Harveyn4444/cubesat-reaction-wheel/assets/img/motor-encoder.png

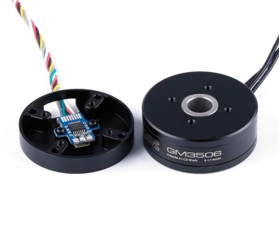
assets/img/motor-encoder.png
