Harveyn4444/cubesat-reaction-wheel/assets/img/mpu6050.jpeg

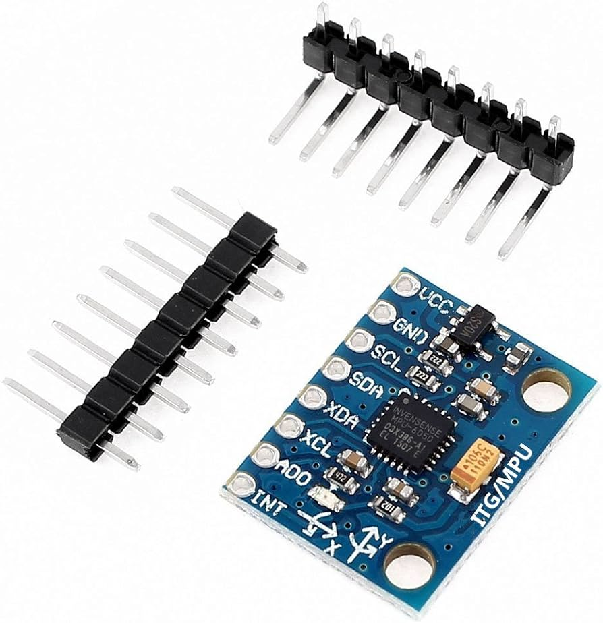
assets/img/mpu6050.jpeg
