Harveyn4444/cubesat-reaction-wheel/assets/img/teensy4.jpeg

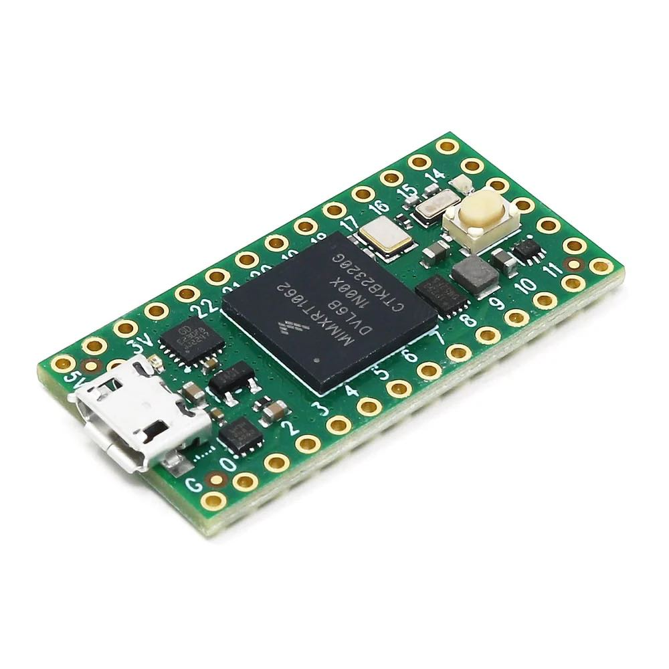
assets/img/teensy4.jpeg
