Harveyn4444/cubesat-reaction-wheel/assets/img/wheel.png

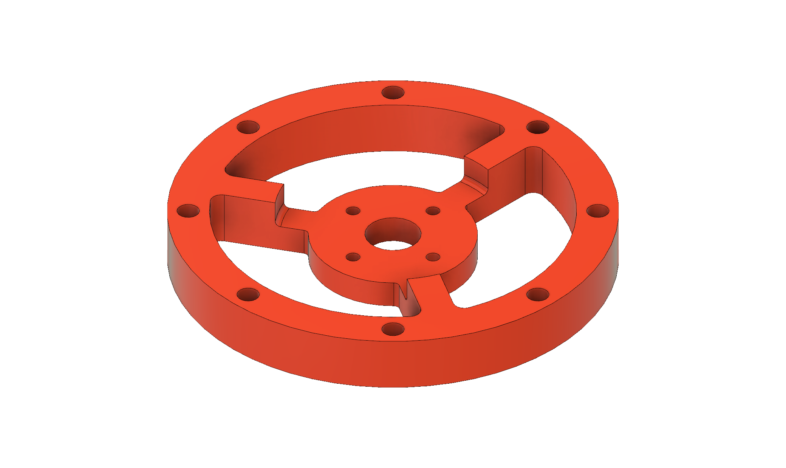
assets/img/wheel.png
