Harveyn4444/cubesat-reaction-wheel/code/data-logging/data/open-loop-rc/open-loop-velocity.png

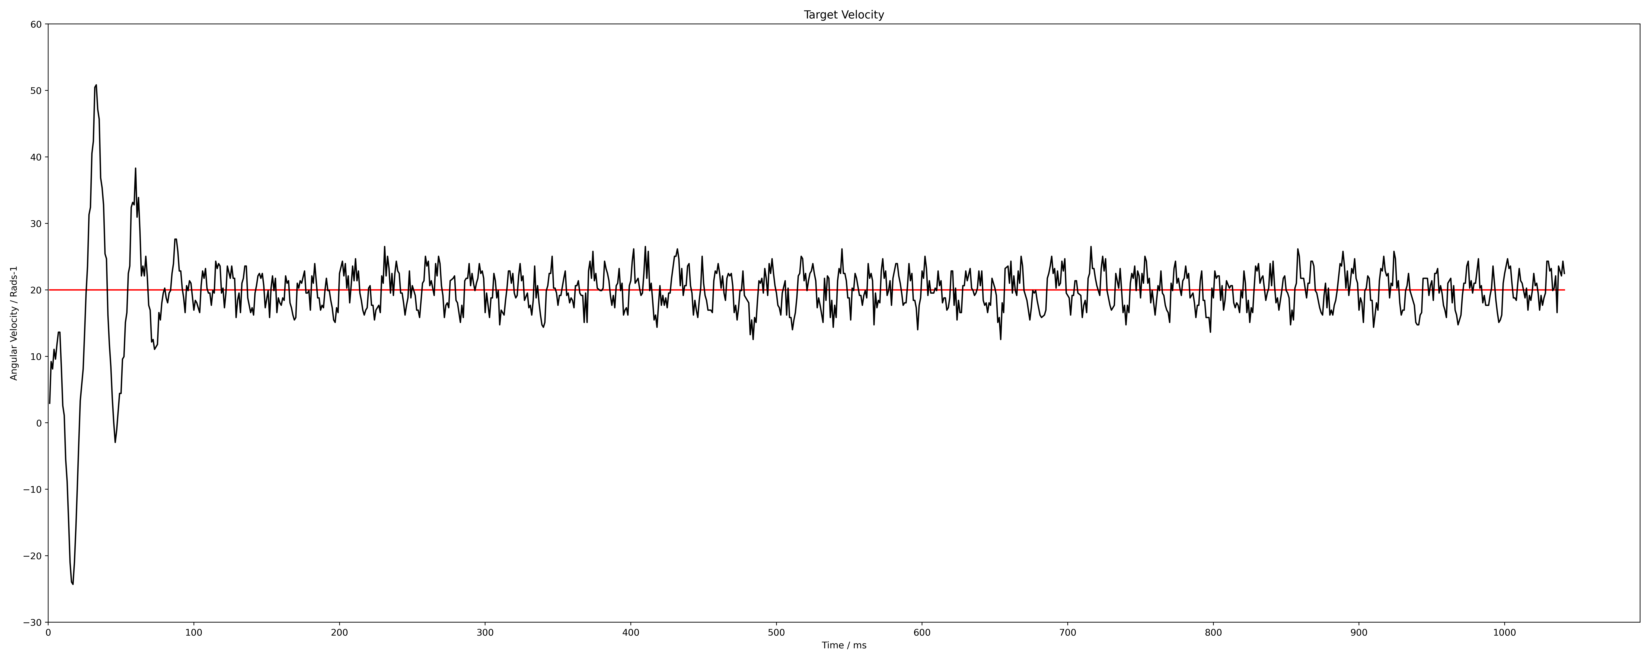
code/data-logging/data/open-loop-rc/open-loop-velocity.png
