Harveyn4444/cubesat-reaction-wheel/code/data-logging/data/pid-velocity/pid-1-0-0.png

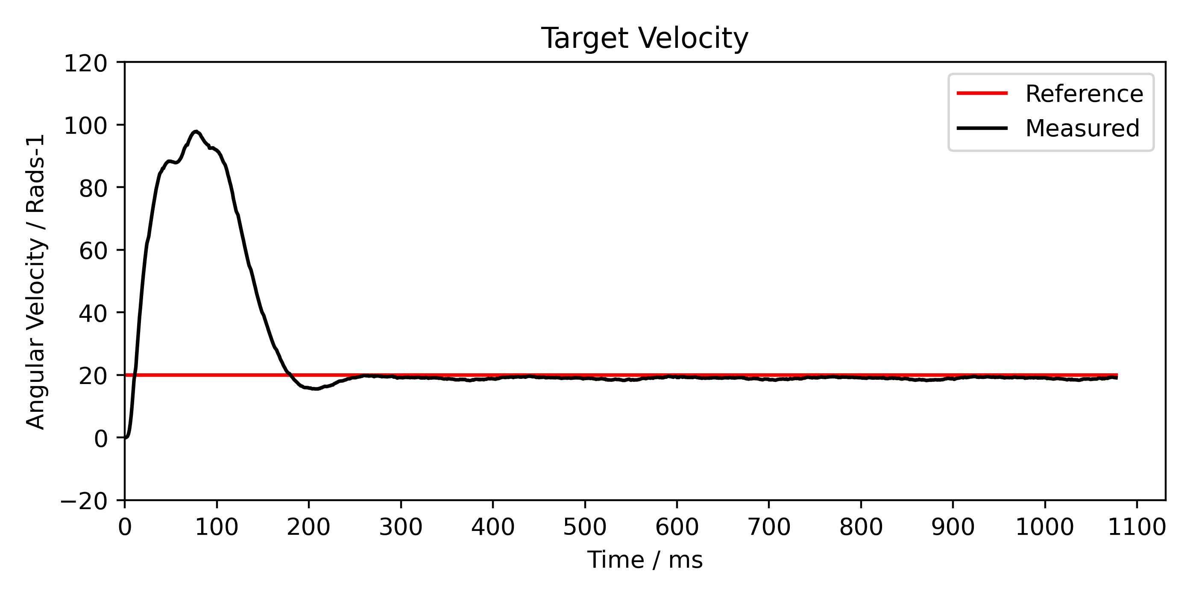
code/data-logging/data/pid-velocity/pid-1-0-0.png
