Harveyn4444/cubesat-reaction-wheel/code/data-logging/data/pid-velocity/pid-1-10-0.png

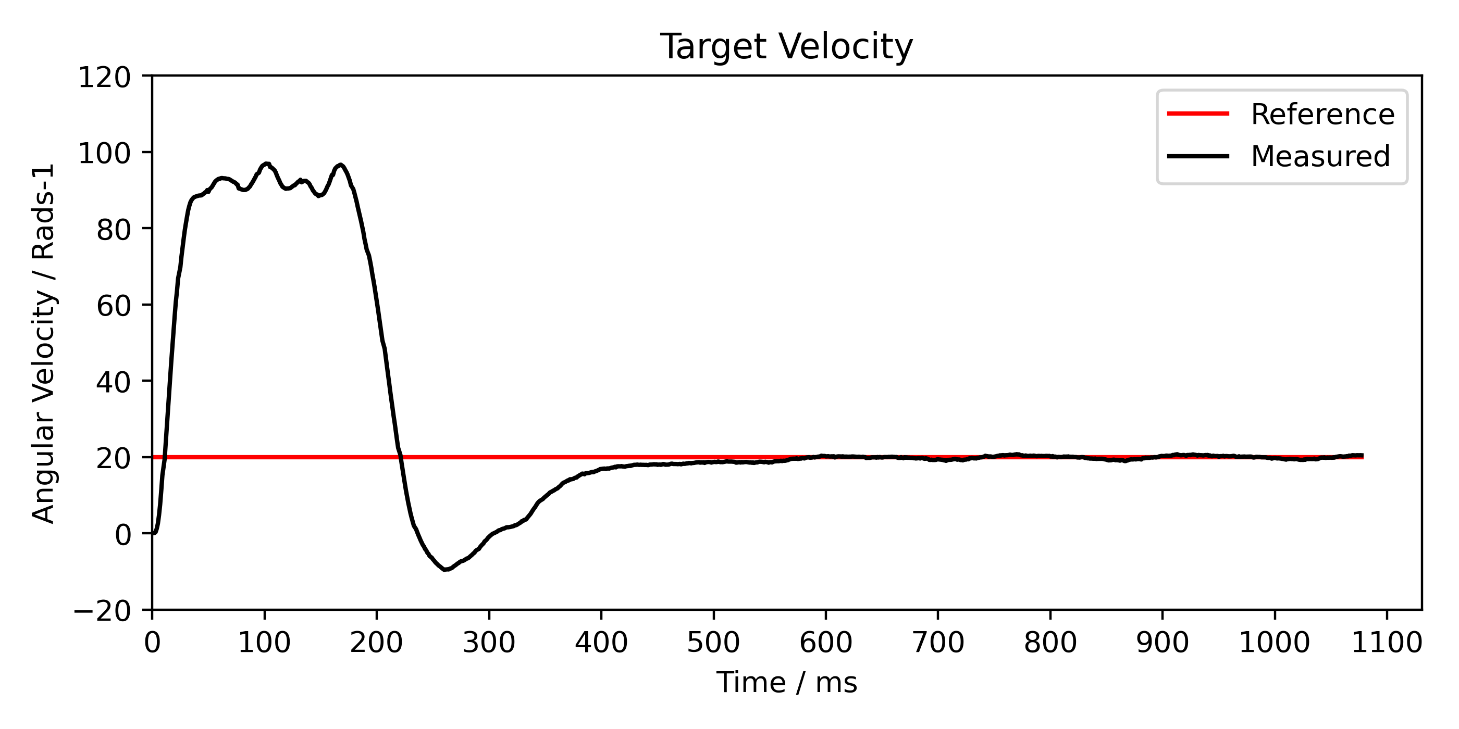
code/data-logging/data/pid-velocity/pid-1-10-0.png
