Harveyn4444/cubesat-reaction-wheel/code/data-logging/data/pid-torque/measured-torque-test-2.csv

Time | TargetVelocity | TargetTorque | Measured | Error | alpha | torque
0 | 20.00 | 0.1899 | 0.00 | 20.00 | 0.0006 | 0.0015
1 | 20.00 | 0.1899 | 0.00 | 20.00 | -0.0001 | -0.0002
2 | 20.00 | 0.1899 | 0.00 | 20.00 | -0.0001 | -0.0001
3 | 20.00 | 0.1899 | 0.11 | 19.89 | 0.0266 | 0.0638
4 | 20.00 | 0.1899 | 0.24 | 19.76 | 0.0328 | 0.0787
5 | 20.00 | 0.1899 | 0.39 | 19.61 | 0.0384 | 0.0921
6 | 20.00 | 0.1899 | 0.57 | 19.43 | 0.0434 | 0.1042
7 | 20.00 | 0.1899 | 0.58 | 19.42 | 0.0036 | 0.0086
8 | 20.00 | 0.1899 | 0.95 | 19.05 | 0.0920 | 0.2208
9 | 20.00 | 0.1899 | 1.21 | 18.79 | 0.0650 | 0.1561
11 | 20.00 | 0.1899 | 1.34 | 18.66 | 0.0319 | 0.0766
12 | 20.00 | 0.1899 | 1.66 | 18.34 | 0.0820 | 0.1967
13 | 20.00 | 0.1899 | 1.85 | 18.15 | 0.0472 | 0.1132
14 | 20.00 | 0.1899 | 2.17 | 17.83 | 0.0779 | 0.1871
15 | 20.00 | 0.1899 | 2.41 | 17.59 | 0.0613 | 0.1470
16 | 20.00 | 0.1899 | 2.74 | 17.26 | 0.0818 | 0.1963
17 | 20.00 | 0.1899 | 3.03 | 16.97 | 0.0736 | 0.1766
18 | 20.00 | 0.1899 | 3.33 | 16.67 | 0.0751 | 0.1803
19 | 20.00 | 0.1899 | 3.67 | 16.33 | 0.0854 | 0.2048
20 | 20.00 | 0.1899 | 3.84 | 16.16 | 0.0413 | 0.0992
21 | 20.00 | 0.1899 | 4.17 | 15.83 | 0.0816 | 0.1958
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
