Harveyn4444/cubesat-reaction-wheel/code/data-logging/data/pid-torque/pid-torque-test-1-0-0.csv

Time | Target | Measured | Error
0 | 20.00 | 0.00 | 20.00
1 | 20.00 | 0.04 | 19.96
2 | 20.00 | 0.14 | 19.86
3 | 20.00 | 0.34 | 19.66
4 | 20.00 | 0.70 | 19.30
5 | 20.00 | 1.31 | 18.69
6 | 20.00 | 1.92 | 18.08
7 | 20.00 | 2.55 | 17.45
8 | 20.00 | 3.26 | 16.74
9 | 20.00 | 3.89 | 16.11
10 | 20.00 | 4.79 | 15.21
12 | 20.00 | 5.45 | 14.55
13 | 20.00 | 6.01 | 13.99
14 | 20.00 | 6.79 | 13.21
15 | 20.00 | 7.36 | 12.64
16 | 20.00 | 8.05 | 11.95
17 | 20.00 | 8.70 | 11.30
18 | 20.00 | 9.26 | 10.74
19 | 20.00 | 9.86 | 10.14
20 | 20.00 | 10.45 | 9.55
21 | 20.00 | 10.90 | 9.10
22 | 20.00 | 11.41 | 8.59
23 | 20.00 | 11.87 | 8.13
24 | 20.00 | 12.50 | 7.50
26 | 20.00 | 12.96 | 7.04
27 | 20.00 | 13.55 | 6.45
28 | 20.00 | 13.80 | 6.20
29 | 20.00 | 14.30 | 5.70
30 | 20.00 | 14.51 | 5.49
31 | 20.00 | 14.81 | 5.19
32 | 20.00 | 15.14 | 4.86
33 | 20.00 | 15.27 | 4.73
34 | 20.00 | 15.59 | 4.41
35 | 20.00 | 15.74 | 4.26
36 | 20.00 | 16.02 | 3.98
37 | 20.00 | 16.16 | 3.84
38 | 20.00 | 16.47 | 3.53
40 | 20.00 | 16.68 | 3.32
41 | 20.00 | 16.93 | 3.07
42 | 20.00 | 16.99 | 3.01
43 | 20.00 | 17.21 | 2.79
44 | 20.00 | 17.34 | 2.66
45 | 20.00 | 17.36 | 2.64
46 | 20.00 | 17.48 | 2.52
47 | 20.00 | 17.58 | 2.42
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
