Harveyn4444/cubesat-reaction-wheel/code/data-logging/data/pid-torque/pid-torque-test-1-20-0.csv

Time | Target | Measured | Error
0 | 20.00 | -0.00 | 20.00
1 | 20.00 | 0.03 | 19.97
2 | 20.00 | 0.03 | 19.97
3 | 20.00 | 0.24 | 19.76
4 | 20.00 | 0.82 | 19.18
5 | 20.00 | 1.38 | 18.62
6 | 20.00 | 2.03 | 17.97
7 | 20.00 | 2.64 | 17.36
8 | 20.00 | 3.45 | 16.55
9 | 20.00 | 4.28 | 15.72
10 | 20.00 | 4.96 | 15.04
12 | 20.00 | 5.78 | 14.22
13 | 20.00 | 6.52 | 13.48
14 | 20.00 | 7.19 | 12.81
15 | 20.00 | 8.00 | 12.00
16 | 20.00 | 8.62 | 11.38
17 | 20.00 | 9.36 | 10.64
18 | 20.00 | 9.89 | 10.11
19 | 20.00 | 10.46 | 9.54
20 | 20.00 | 11.06 | 8.94
21 | 20.00 | 11.63 | 8.37
22 | 20.00 | 12.10 | 7.90
23 | 20.00 | 12.71 | 7.29
24 | 20.00 | 13.15 | 6.85
26 | 20.00 | 13.69 | 6.31
27 | 20.00 | 14.17 | 5.83
28 | 20.00 | 14.57 | 5.43
29 | 20.00 | 15.07 | 4.93
30 | 20.00 | 15.38 | 4.62
31 | 20.00 | 15.58 | 4.42
32 | 20.00 | 15.95 | 4.05
33 | 20.00 | 16.21 | 3.79
34 | 20.00 | 16.44 | 3.56
35 | 20.00 | 16.72 | 3.28
36 | 20.00 | 16.97 | 3.03
37 | 20.00 | 17.12 | 2.88
38 | 20.00 | 17.26 | 2.74
40 | 20.00 | 17.64 | 2.36
41 | 20.00 | 17.83 | 2.17
42 | 20.00 | 17.94 | 2.06
43 | 20.00 | 18.14 | 1.86
44 | 20.00 | 18.21 | 1.79
45 | 20.00 | 18.53 | 1.47
46 | 20.00 | 18.52 | 1.48
47 | 20.00 | 18.59 | 1.41
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
