Harveyn4444/cubesat-reaction-wheel/code/data-logging/data/open-loop-rc/testing-rc.png

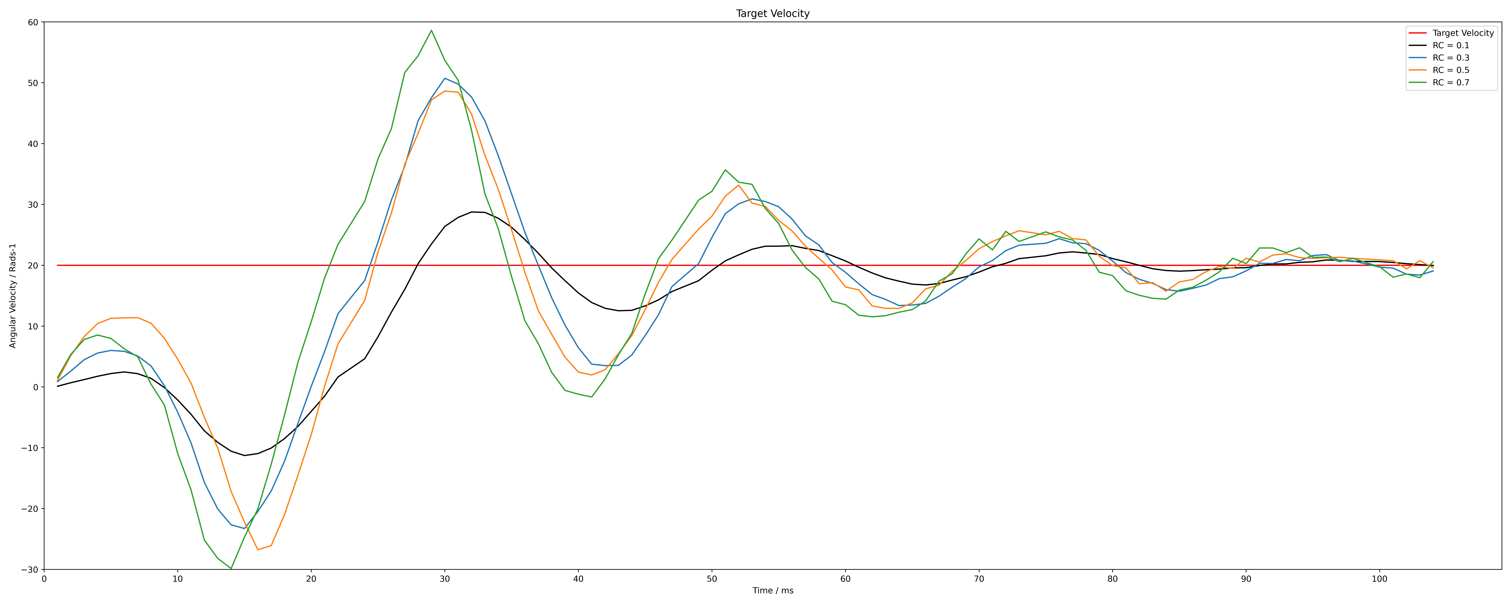
code/data-logging/data/open-loop-rc/testing-rc.png
