Harveyn4444/cubesat-reaction-wheel/code/data-logging/data/open-loop/open-loop-velocity-test.png

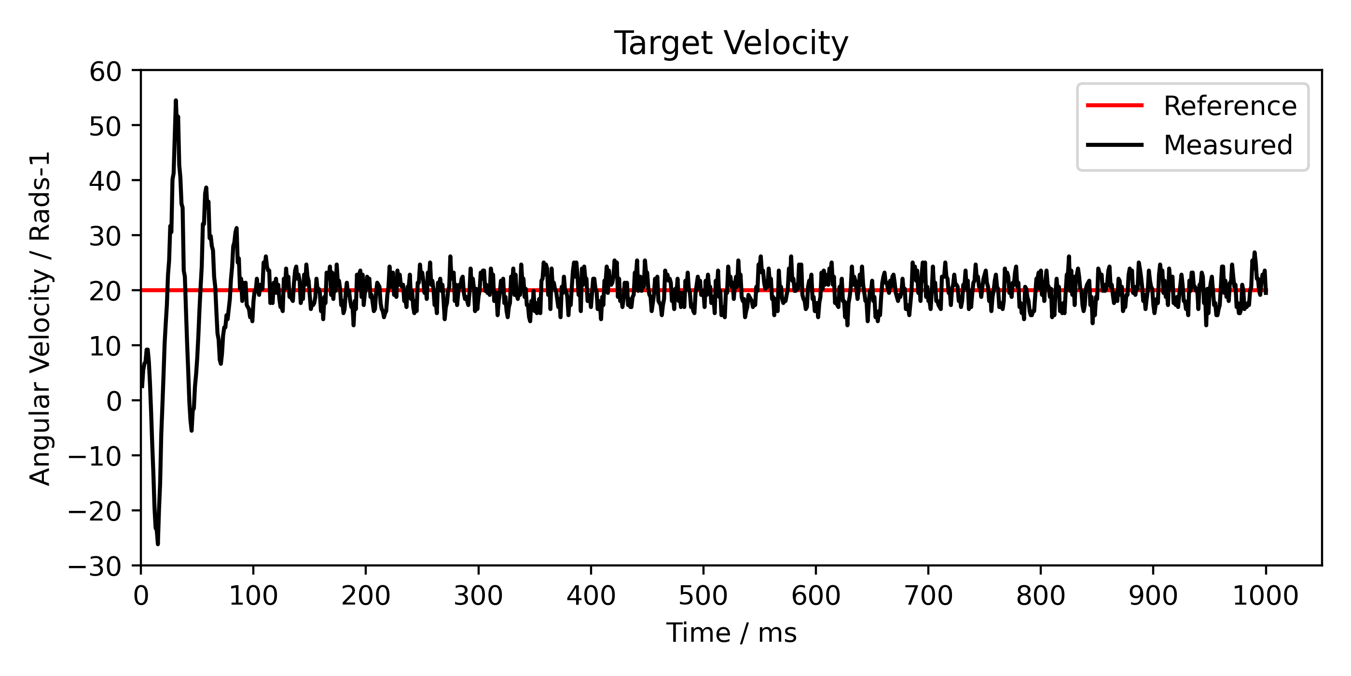
code/data-logging/data/open-loop/open-loop-velocity-test.png
