Harveyn4444/cubesat-reaction-wheel/code/data-logging/data/pid-torque/pid-alpha-test.png

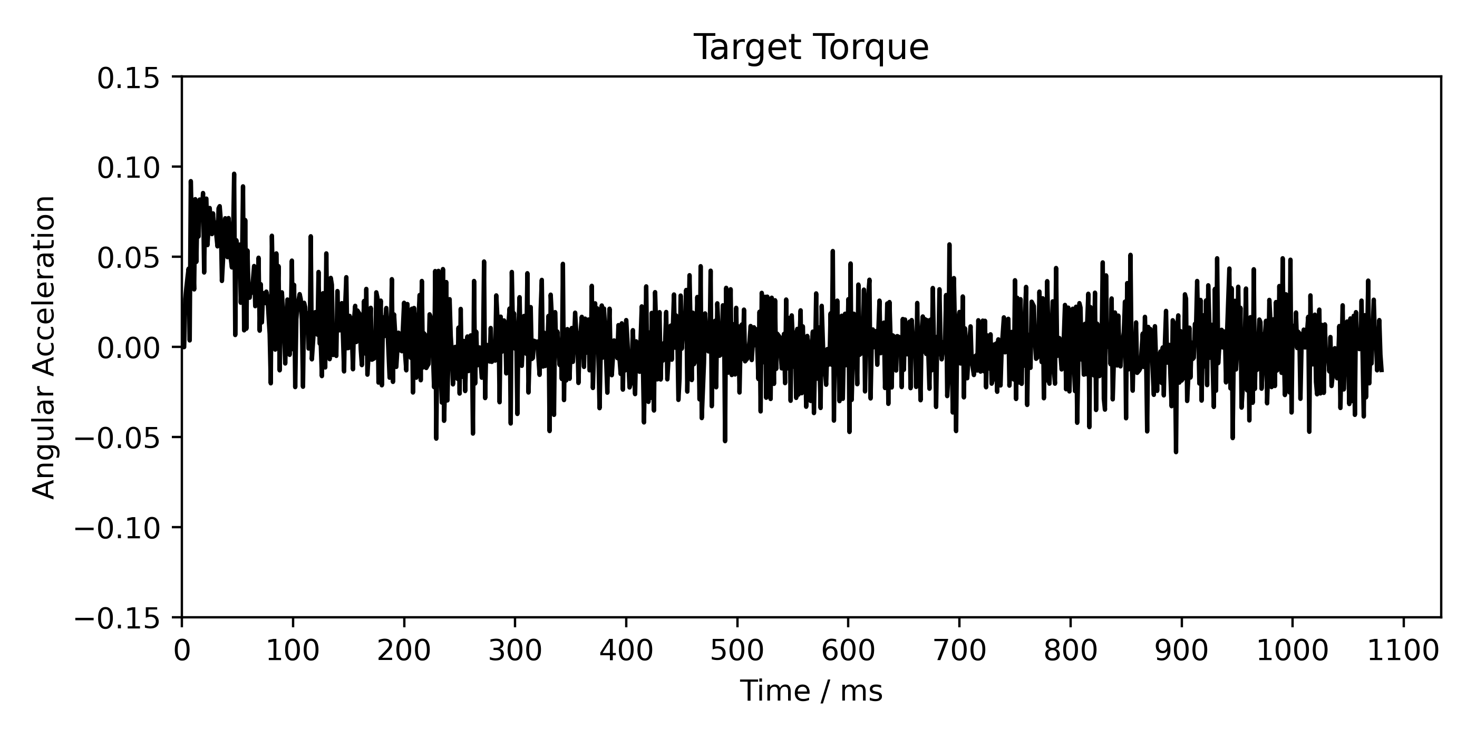
code/data-logging/data/pid-torque/pid-alpha-test.png
