Harveyn4444/cubesat-reaction-wheel/code/data-logging/data/pid-torque/pid-torque-measure-1-10-0.png

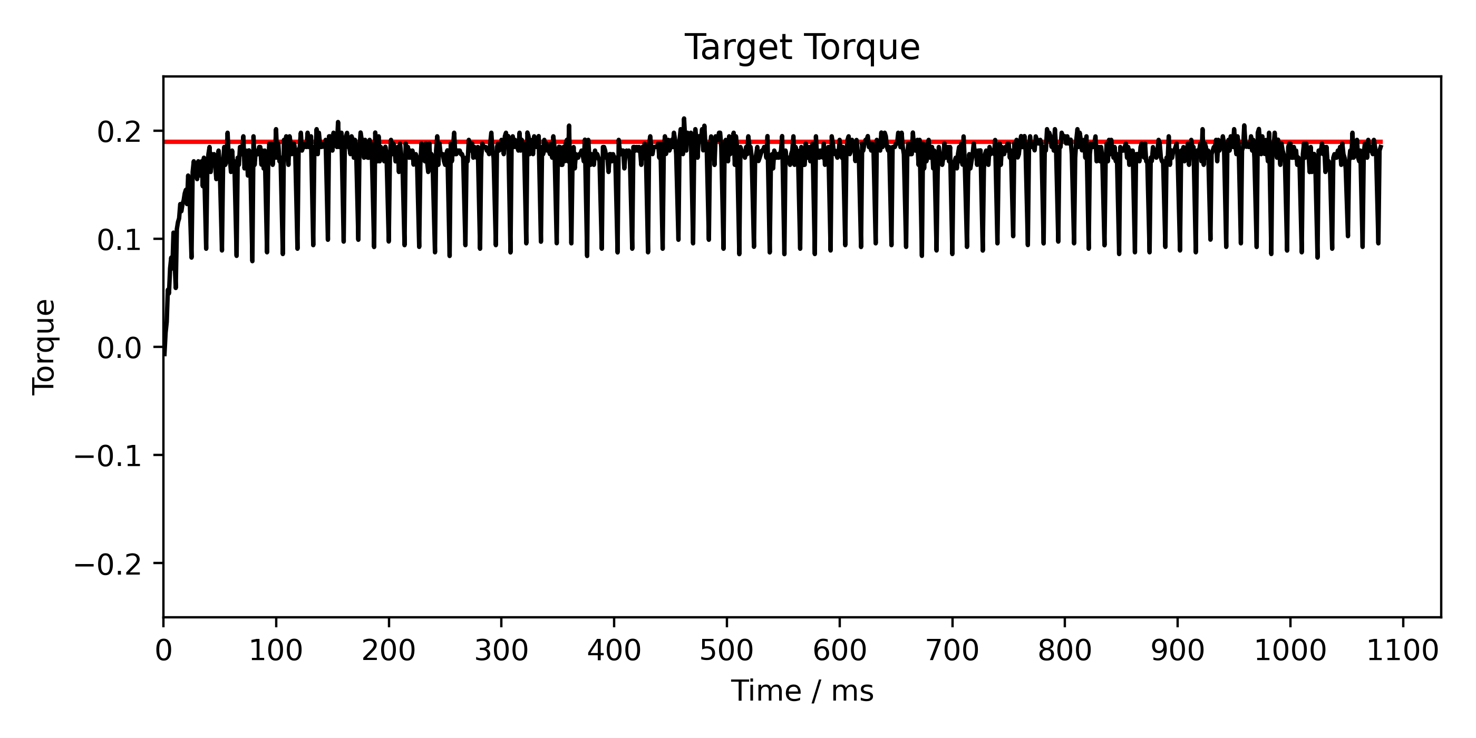
code/data-logging/data/pid-torque/pid-torque-measure-1-10-0.png
