Harveyn4444/cubesat-reaction-wheel/code/data-logging/data/pid-torque/pid-torque-test-2.png

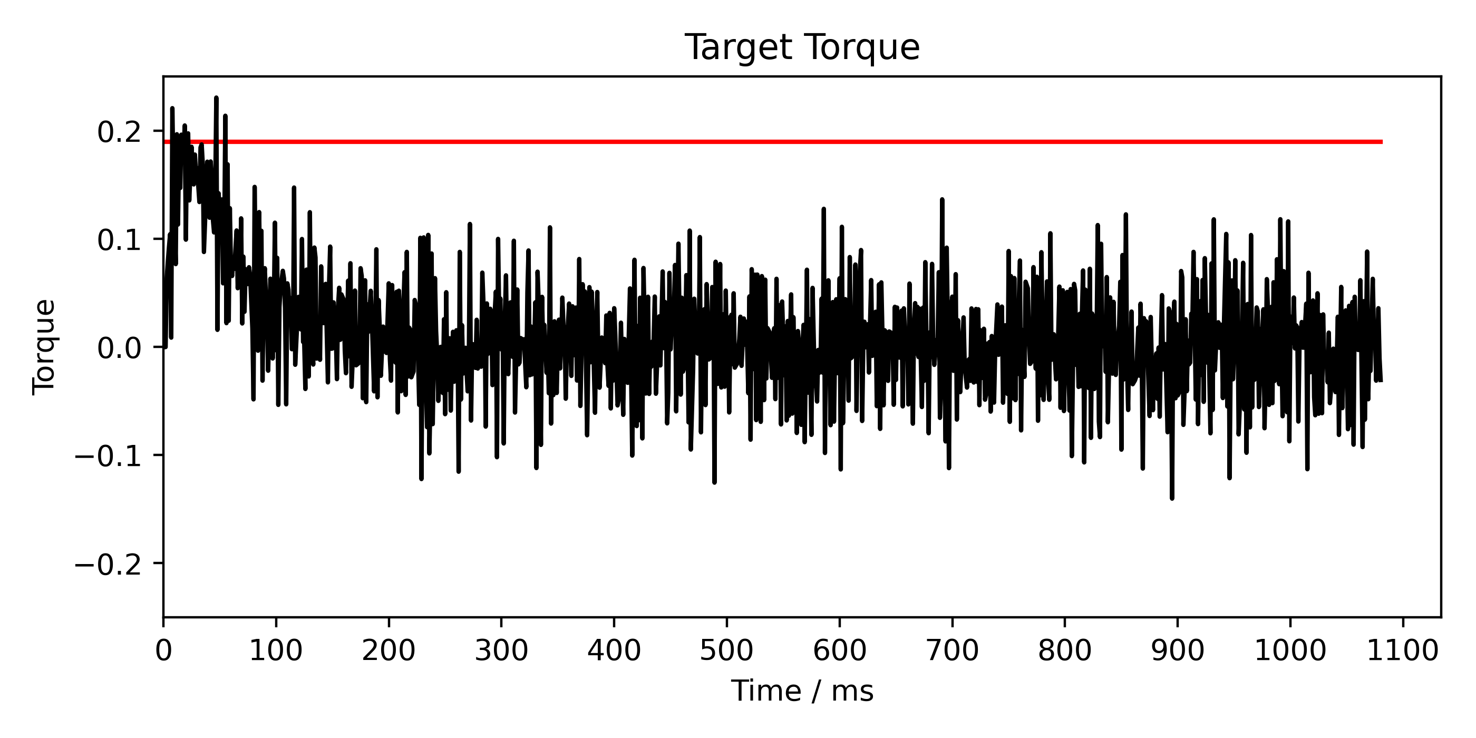
code/data-logging/data/pid-torque/pid-torque-test-2.png
