Harveyn4444/cubesat-reaction-wheel/code/data-logging/data/testing-rc.png

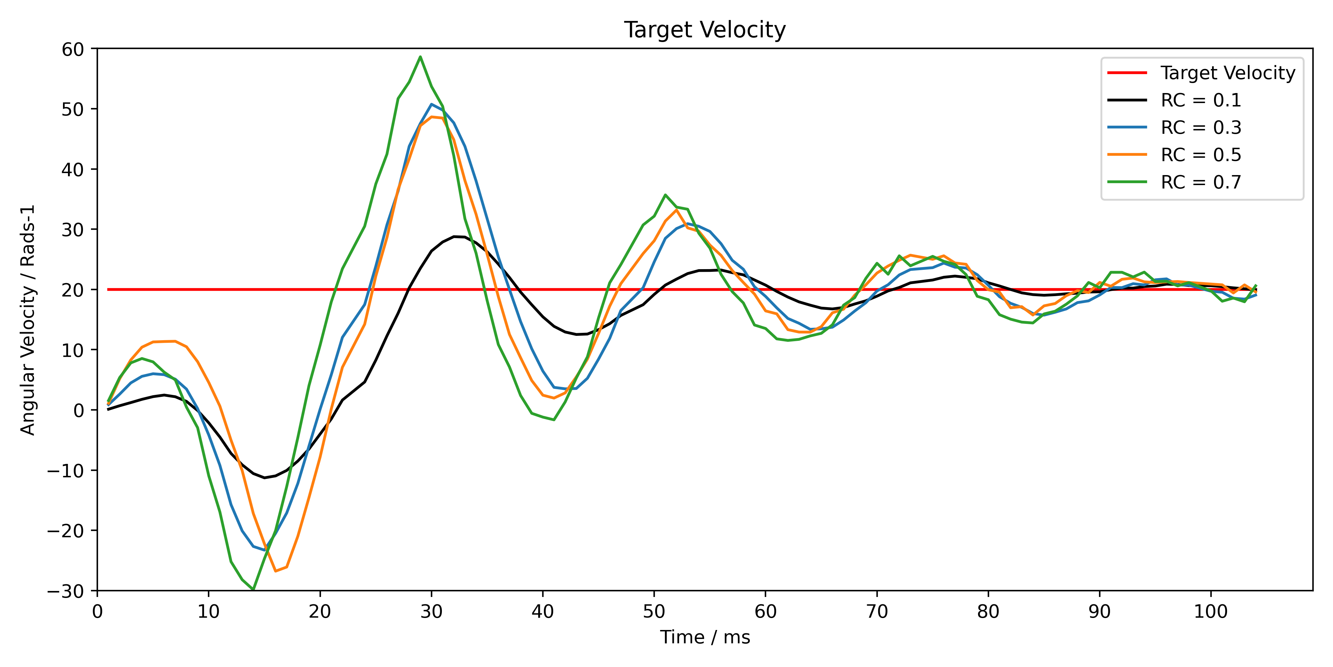
code/data-logging/data/testing-rc.png
